thanhtuan2503/digitalSystemBoard/digitalSystemBoard/3dSymbol/Fuse.step

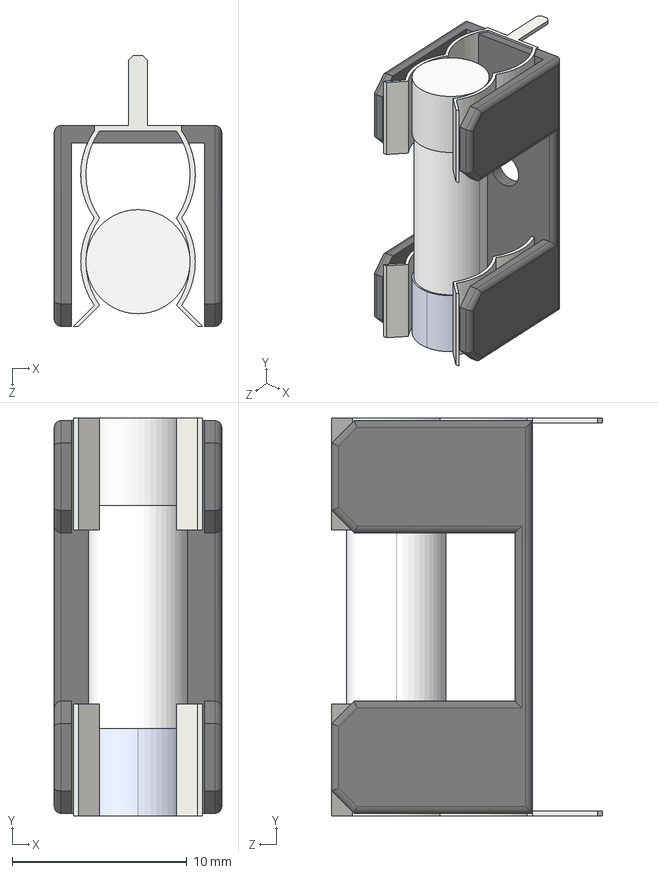
[picture p18: CAD file, 2022-01-30]
digitalSystemBoard/3dSymbol/Fuse.step
9.60 x 22.8 x 15.5 mm
Fuseholder_Cylinder-5x20mm_Schurter_0031_8201_Horizontal_Open
FuseTube^Fuse
