thanhtuan2503/digitalSystemBoard/digitalSystemBoard/3dSymbol/DS1013 (IDC CONNFLY)/DS1013-50S (IDC-50MS CONNFLY).step

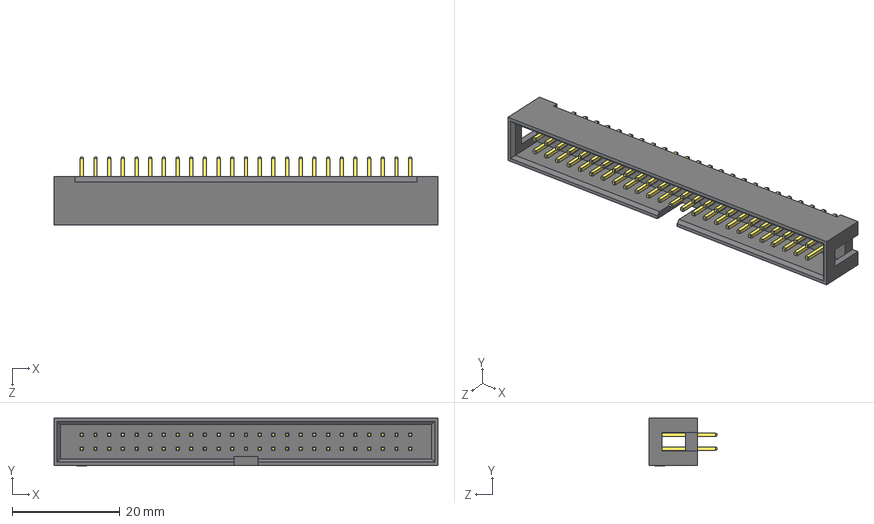
[picture p19: CAD file, 2022-01-30]
digitalSystemBoard/3dSymbol/DS1013 (IDC CONNFLY)/DS1013-50S (IDC-50MS CONNFLY).step
71.3 x 8.90 x 12.6 mm
