thanhtuan2503/digitalSystemBoard/digitalSystemBoard/3dSymbol/DS1013 (IDC CONNFLY)/DS1013-20S (IDC-20MS CONNFLY).stp

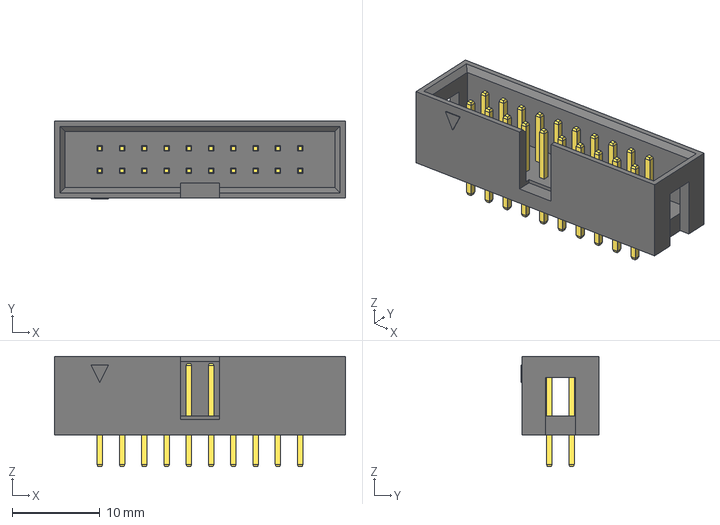
[picture p20: CAD file, 2022-01-30]
digitalSystemBoard/3dSymbol/DS1013 (IDC CONNFLY)/DS1013-20S (IDC-20MS CONNFLY).stp
33.2 x 8.90 x 12.6 mm
