thanhtuan2503/digitalSystemBoard/digitalSystemBoard/3dSymbol/Modul3d_V3.step

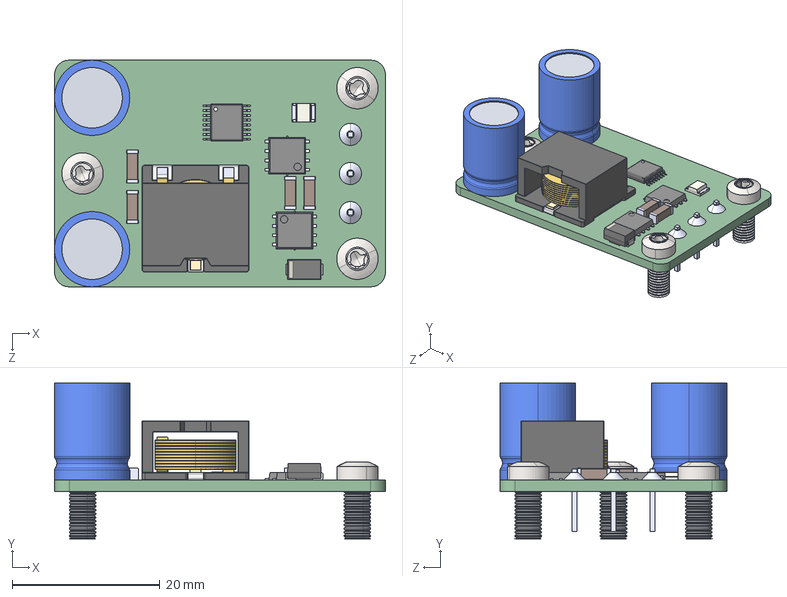
[picture p21: CAD file, 2022-01-30]
digitalSystemBoard/3dSymbol/Modul3d_V3.step
44.9 x 21.1 x 30.7 mm
Part1.step
Inductor.step
TPCA8053-H.step x 2
tu.step x 2
TPS40057PWPRG4.step
D_SMA.step
LED_1210_3225Metric.step
tu_Lon.step x 4
hexalobular socket pan head_iso_ISO 14583 - M3 x 8 x 7 - 4.8-S x 3
Solder^Modul3d
