thanhtuan2503/digitalSystemBoard/digitalSystemBoard/3dSymbol/DS1013 (IDC CONNFLY)/DS1013-26S (IDC-26MS CONNFLY).stp

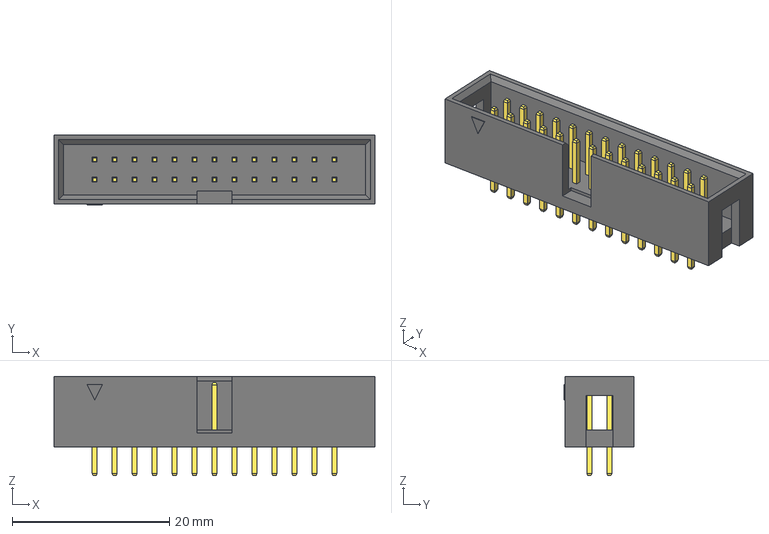
[picture p22: CAD file, 2022-01-30]
digitalSystemBoard/3dSymbol/DS1013 (IDC CONNFLY)/DS1013-26S (IDC-26MS CONNFLY).stp
40.8 x 8.90 x 12.6 mm
