thanhtuan2503/digitalSystemBoard/digitalSystemBoard/3dSymbol/Tactal-Switch-SMD-12mmx12mmx4.3mm_V2.step

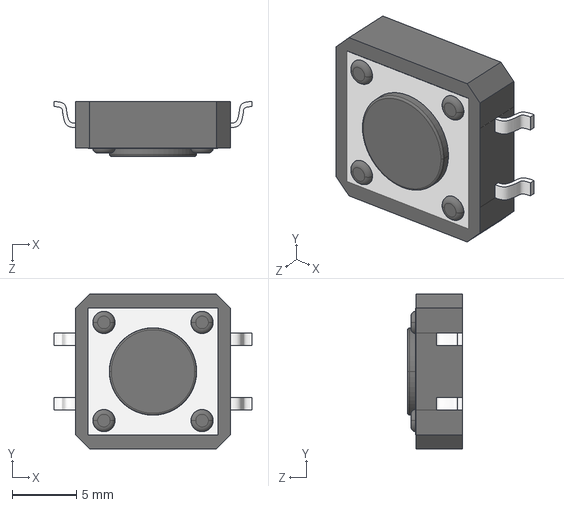
[picture p23: CAD file, 2022-01-30]
digitalSystemBoard/3dSymbol/Tactal-Switch-SMD-12mmx12mmx4.3mm_V2.step
15.4 x 12.0 x 4.25 mm
