thanhtuan2503/digitalSystemBoard/digitalSystemBoard/3dSymbol/DS1013 (IDC CONNFLY)/DS1013-6S (IDC-6MS CONNFLY).stp

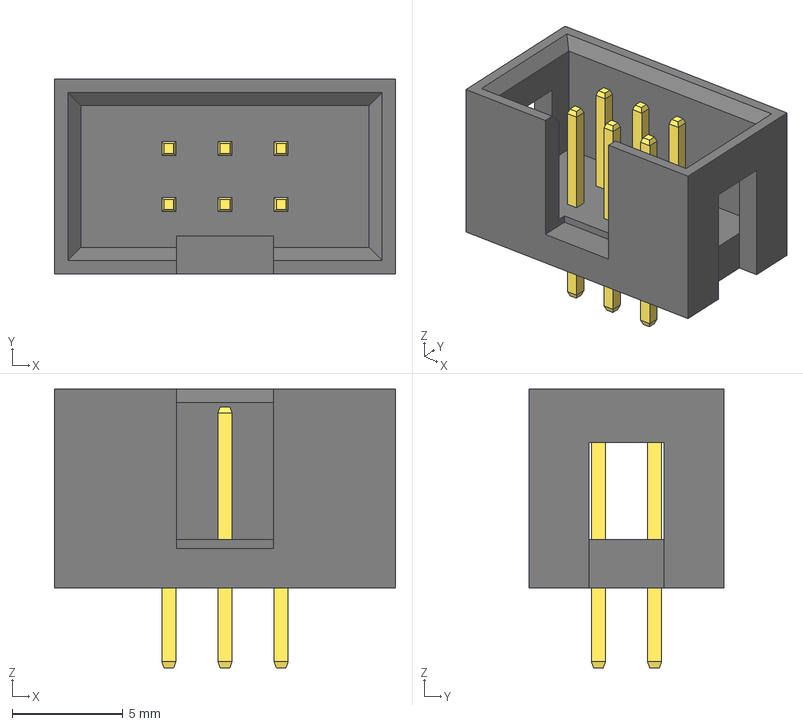
[picture p24: CAD file, 2022-01-30]
digitalSystemBoard/3dSymbol/DS1013 (IDC CONNFLY)/DS1013-6S (IDC-6MS CONNFLY).stp
15.4 x 8.80 x 12.6 mm
