thanhtuan2503/digitalSystemBoard/digitalSystemBoard/3dSymbol/DS1013 (IDC CONNFLY)/DS1013-64S (IDC-64MS CONNFLY).step

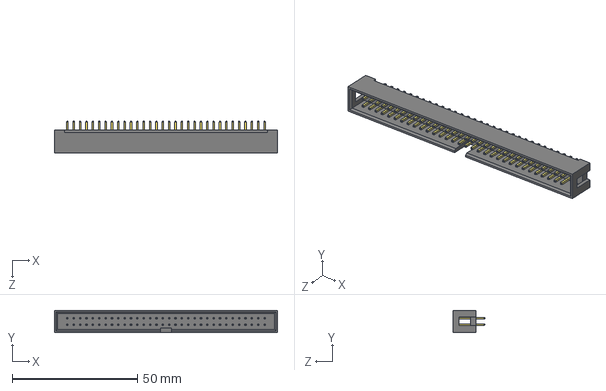
[picture p25: CAD file, 2022-01-30]
digitalSystemBoard/3dSymbol/DS1013 (IDC CONNFLY)/DS1013-64S (IDC-64MS CONNFLY).step
89.1 x 8.90 x 12.6 mm
