thanhtuan2503/digitalSystemBoard/digitalSystemBoard/3dSymbol/DS1013 (IDC CONNFLY)/DS1013-34S (IDC-34MS CONNFLY).step

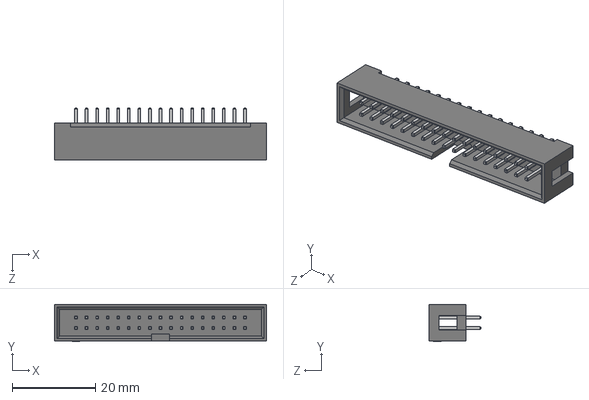
[picture p26: CAD file, 2022-01-30]
digitalSystemBoard/3dSymbol/DS1013 (IDC CONNFLY)/DS1013-34S (IDC-34MS CONNFLY).step
51.0 x 8.90 x 12.6 mm
