thanhtuan2503/digitalSystemBoard/digitalSystemBoard/3dSymbol/DS1013 (IDC CONNFLY)/DS1013-60S (IDC-60MS CONNFLY).step

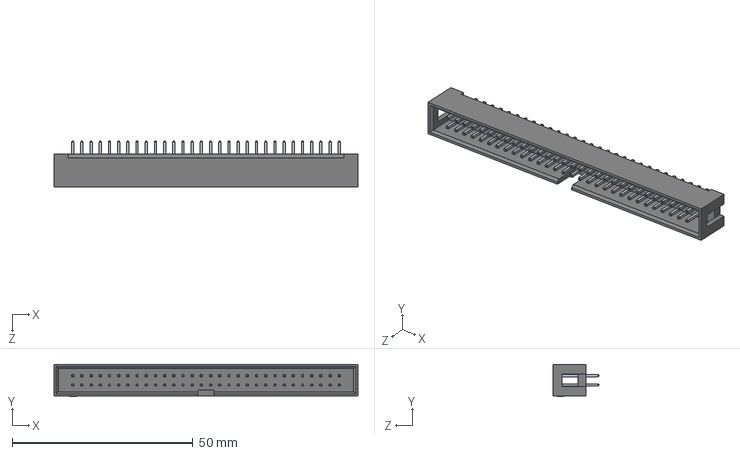
[picture p27: CAD file, 2022-01-30]
digitalSystemBoard/3dSymbol/DS1013 (IDC CONNFLY)/DS1013-60S (IDC-60MS CONNFLY).step
84.0 x 8.90 x 12.6 mm
