thanhtuan2503/digitalSystemBoard/digitalSystemBoard/3dSymbol/PowerSwitch_V2.step

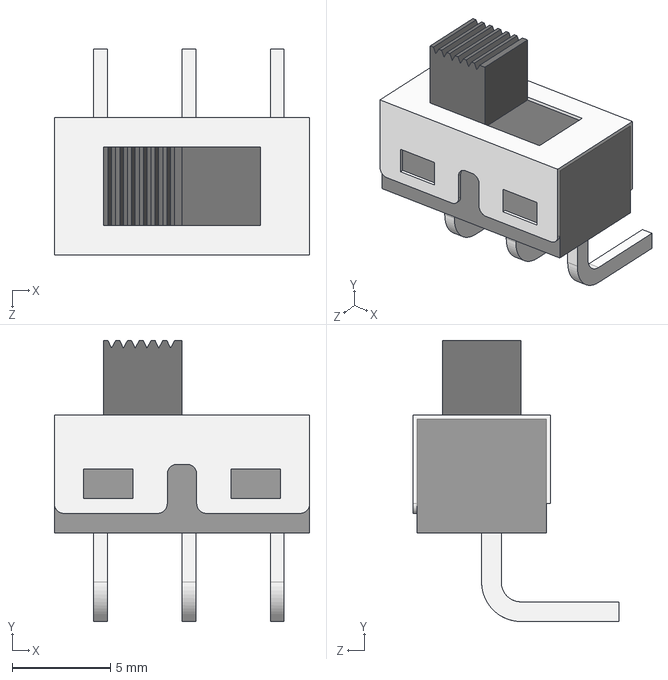
[picture p28: CAD file, 2022-01-30]
digitalSystemBoard/3dSymbol/PowerSwitch_V2.step
13.0 x 14.3 x 10.5 mm
