thanhtuan2503/digitalSystemBoard/digitalSystemBoard/3dSymbol/BC847BW,115.STEP

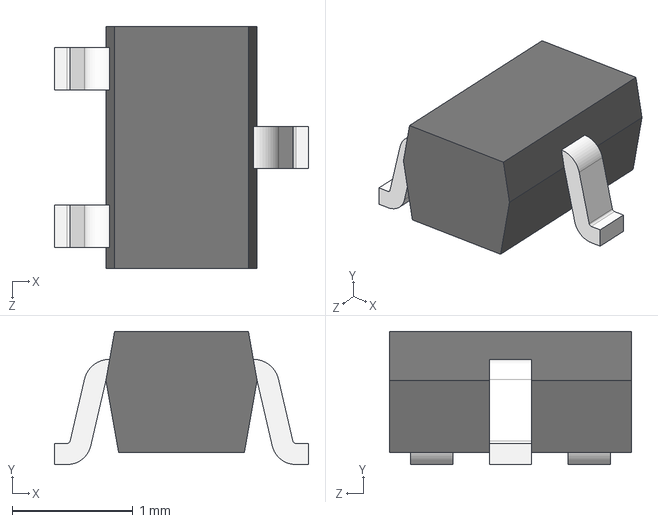
[picture p29: CAD file, 2022-01-30]
digitalSystemBoard/3dSymbol/BC847BW,115.STEP
2.10 x 1.10 x 2.00 mm
