thanhtuan2503/digitalSystemBoard/digitalSystemBoard/3dSymbol/Modul3d.step

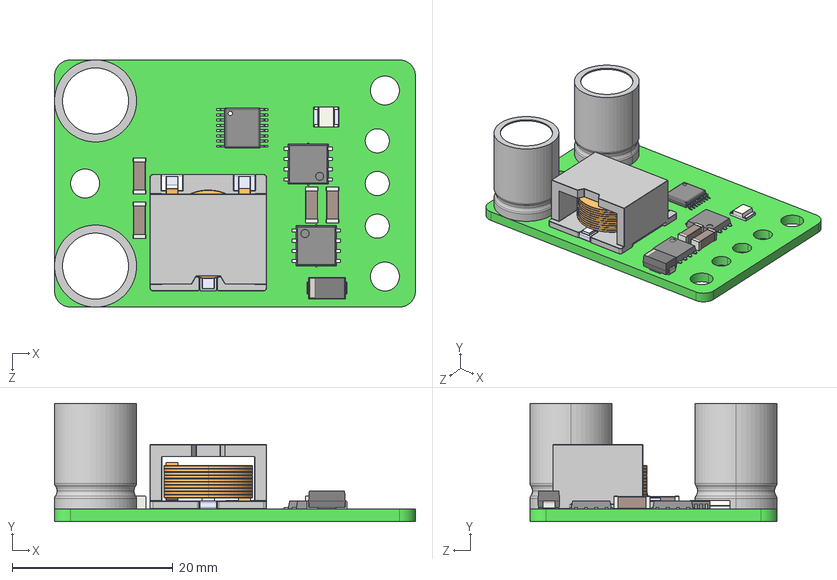
[picture p30: CAD file, 2022-01-30]
digitalSystemBoard/3dSymbol/Modul3d.step
44.9 x 14.7 x 30.7 mm
Inductor
TPCA8053-H x 2
tu x 2
TPS40057PWPRG4
D_SMA
LED_1210_3225Metric
tu_Lon x 4
