thanhtuan2503/digitalSystemBoard/digitalSystemBoard/3dSymbol/DIP_16_PIN_SOCKET.stp

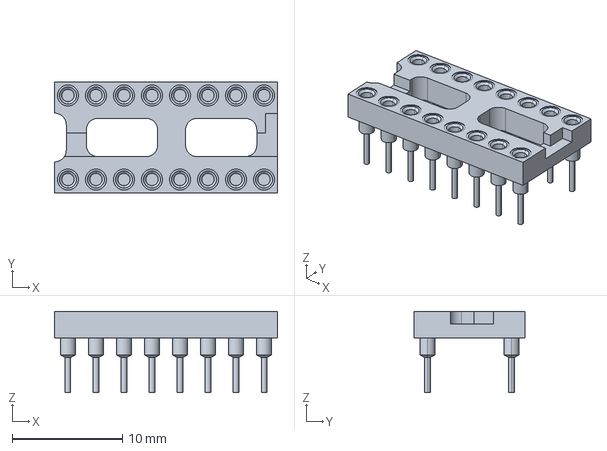
[picture p31: CAD file, 2022-01-30]
digitalSystemBoard/3dSymbol/DIP_16_PIN_SOCKET.stp
20.2 x 10.1 x 7.37 mm
