thanhtuan2503/digitalSystemBoard/digitalSystemBoard/3dSymbol/SC70-6.step

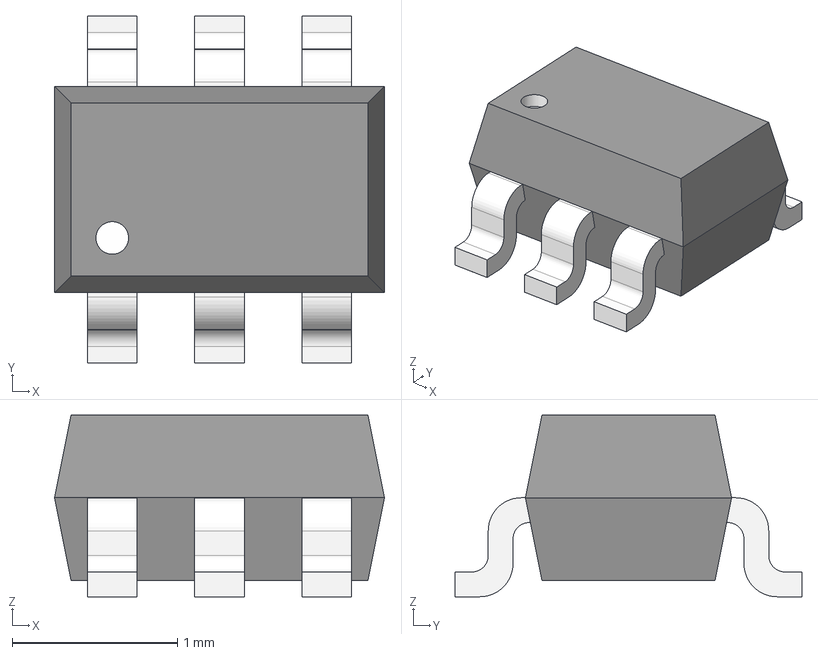
[picture p32: CAD file, 2022-01-30]
digitalSystemBoard/3dSymbol/SC70-6.step
2.00 x 2.10 x 1.10 mm
