thanhtuan2503/digitalSystemBoard/digitalSystemBoard/3dSymbol/FBMH2012HM800-T.STEP

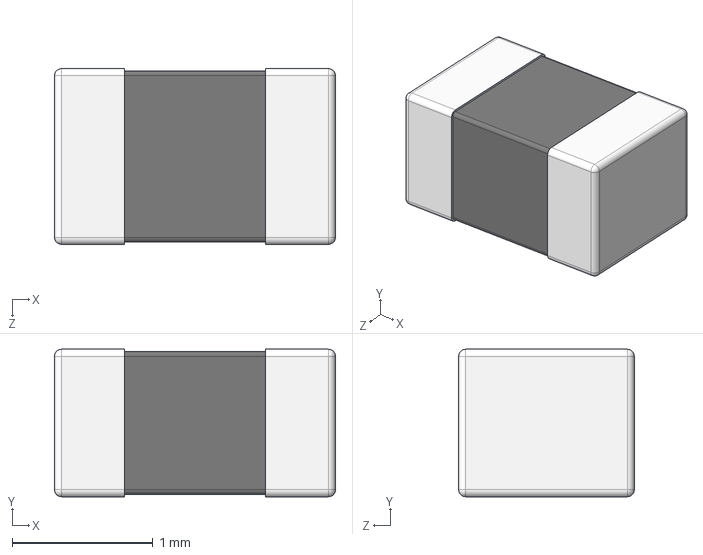
[picture p33: CAD file, 2022-01-30]
digitalSystemBoard/3dSymbol/FBMH2012HM800-T.STEP
2.00 x 1.05 x 1.25 mm
