thanhtuan2503/digitalSystemBoard/digitalSystemBoard/3dSymbol/LM358M.STEP

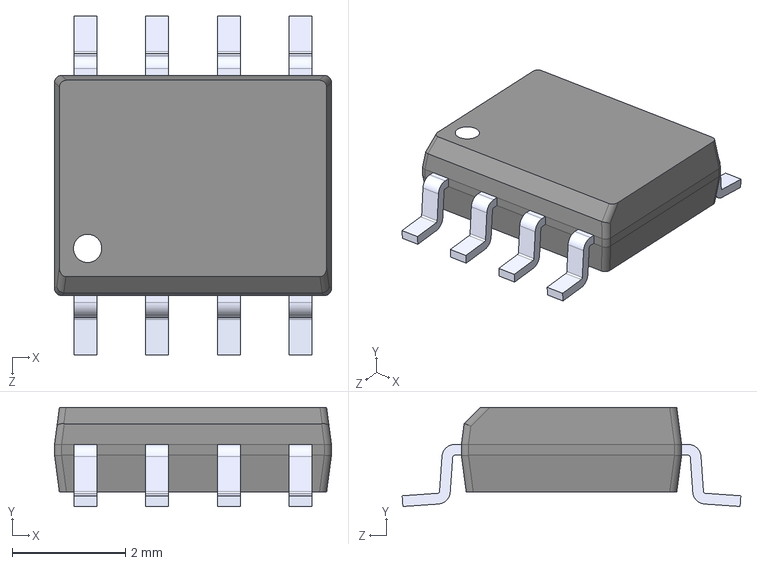
[picture p34: CAD file, 2020-10-29]
digitalSystemBoard/3dSymbol/LM358M.STEP
4.90 x 1.75 x 5.99 mm
