thanhtuan2503/digitalSystemBoard/digitalSystemBoard/3dSymbol/R-PDSO-G4.STEP

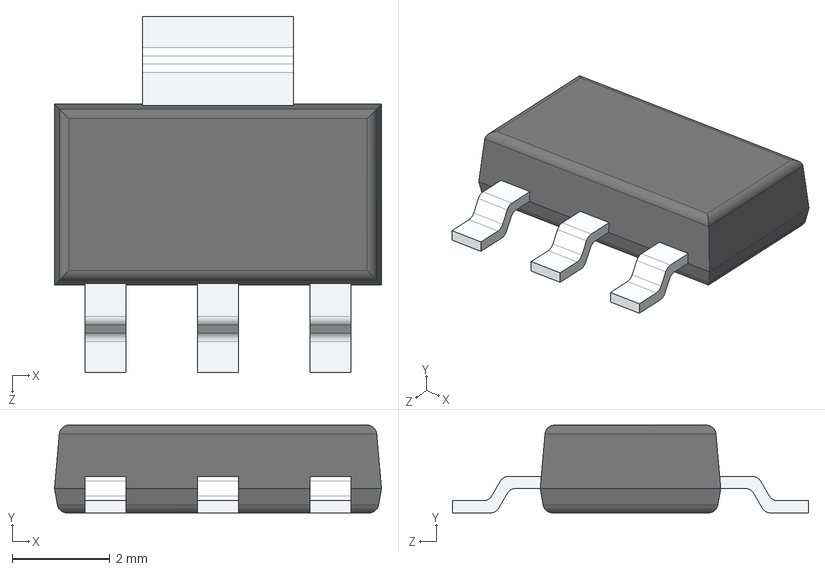
[picture p35: CAD file, 2020-10-24]
digitalSystemBoard/3dSymbol/R-PDSO-G4.STEP
6.70 x 1.80 x 7.30 mm
