thanhtuan2503/digitalSystemBoard/digitalSystemBoard/3dSymbol/to252-3_p4-56_l6-54_w6-04.stp

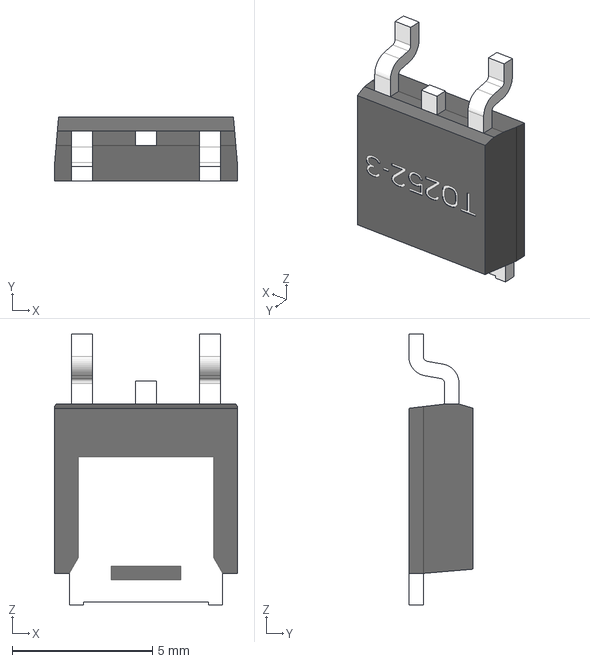
[picture p36: CAD file, 2020-10-24]
digitalSystemBoard/3dSymbol/to252-3_p4-56_l6-54_w6-04.stp
6.54 x 2.30 x 9.67 mm
