thanhtuan2503/digitalSystemBoard/digitalSystemBoard/3dSymbol/SMF05C.STEP

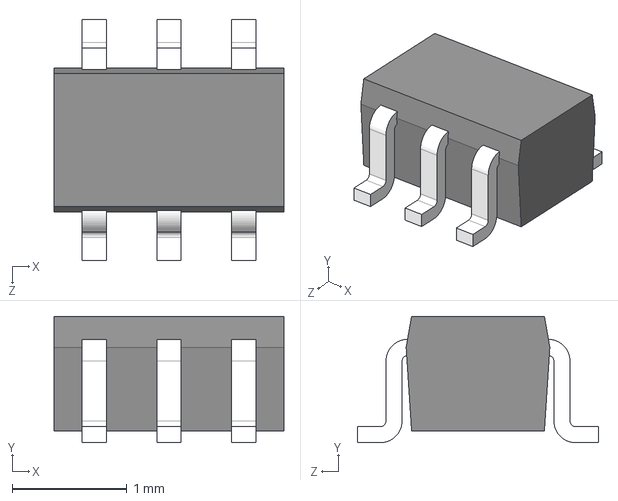
[picture p37: CAD file, 2020-10-22]
digitalSystemBoard/3dSymbol/SMF05C.STEP
2.00 x 1.10 x 2.10 mm
