thanhtuan2503/digitalSystemBoard/digitalSystemBoard/3dSymbol/fdn340p.stp

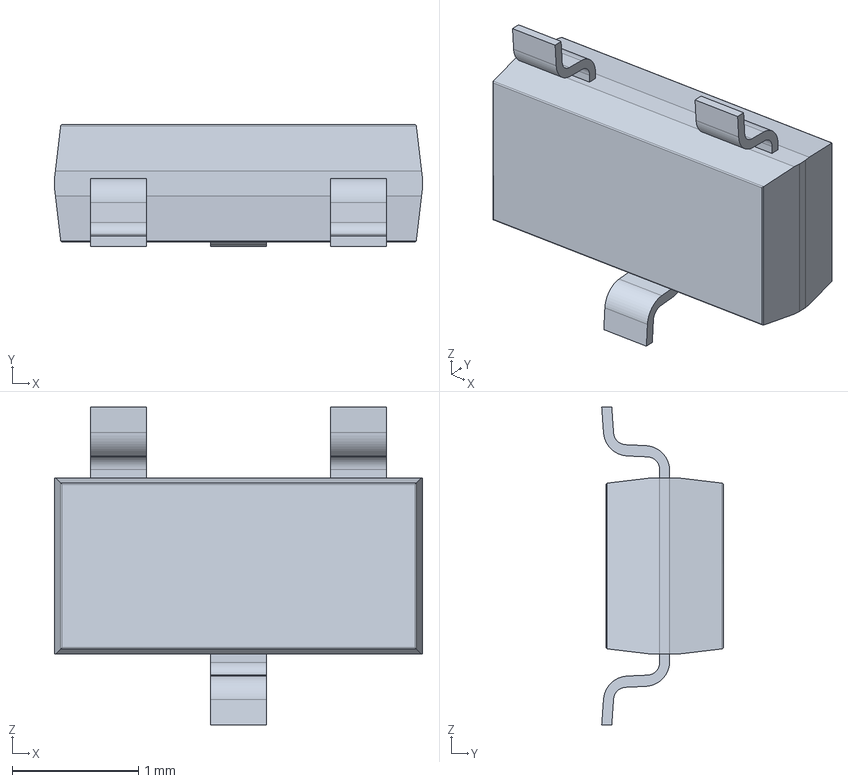
[picture p38: CAD file, 2020-10-21]
digitalSystemBoard/3dSymbol/fdn340p.stp
2.92 x 0.965 x 2.52 mm
