thanhtuan2503/digitalSystemBoard/digitalSystemBoard/3dSymbol/LP2985-33DBVRG4.STEP

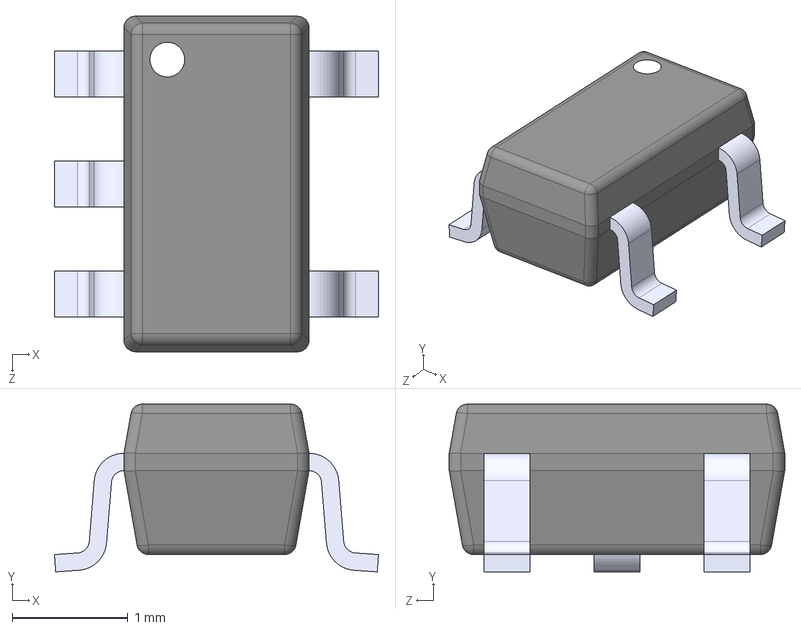
[picture p39: CAD file, 2020-10-21]
digitalSystemBoard/3dSymbol/LP2985-33DBVRG4.STEP
2.80 x 1.45 x 2.90 mm
