thanhtuan2503/digitalSystemBoard/digitalSystemBoard/3dSymbol/OSC5032.STEP

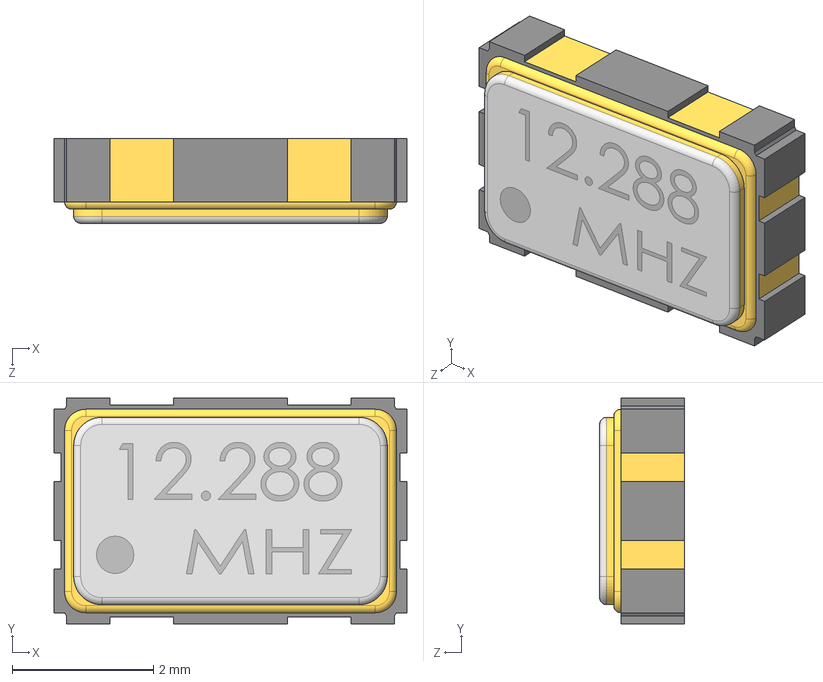
[picture p40: CAD file, 2020-10-21]
digitalSystemBoard/3dSymbol/OSC5032.STEP
5.00 x 3.20 x 1.20 mm
