thanhtuan2503/digitalSystemBoard/digitalSystemBoard/3dSymbol/LMV358AIDGKR.STEP

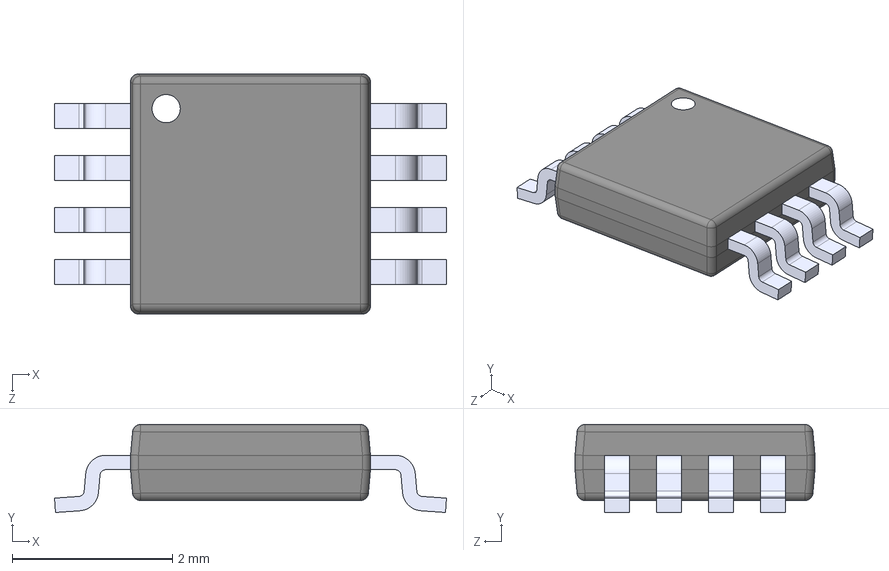
[picture p41: CAD file, 2020-10-21]
digitalSystemBoard/3dSymbol/LMV358AIDGKR.STEP
4.90 x 1.10 x 3.00 mm
