thanhtuan2503/digitalSystemBoard/digitalSystemBoard/3dSymbol/Fuseholder_Cylinder-5x20mm_Schurter_0031_8201_Horizontal_Open.step

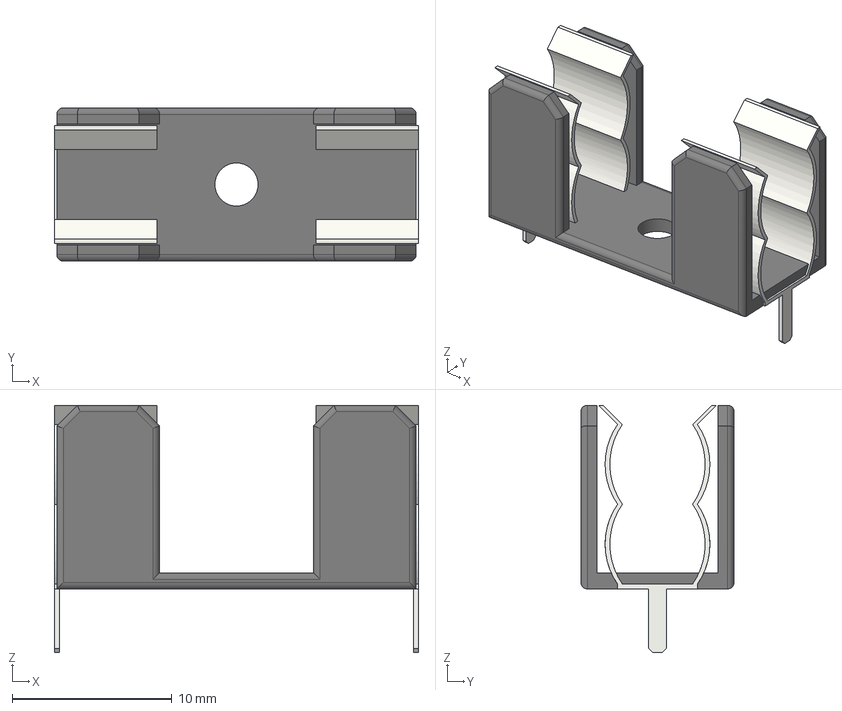
[picture p42: CAD file, 2020-10-21]
digitalSystemBoard/3dSymbol/Fuseholder_Cylinder-5x20mm_Schurter_0031_8201_Horizontal_Open.step
22.8 x 9.60 x 15.5 mm
