thanhtuan2503/digitalSystemBoard/digitalSystemBoard/3dSymbol/LM317T.STEP

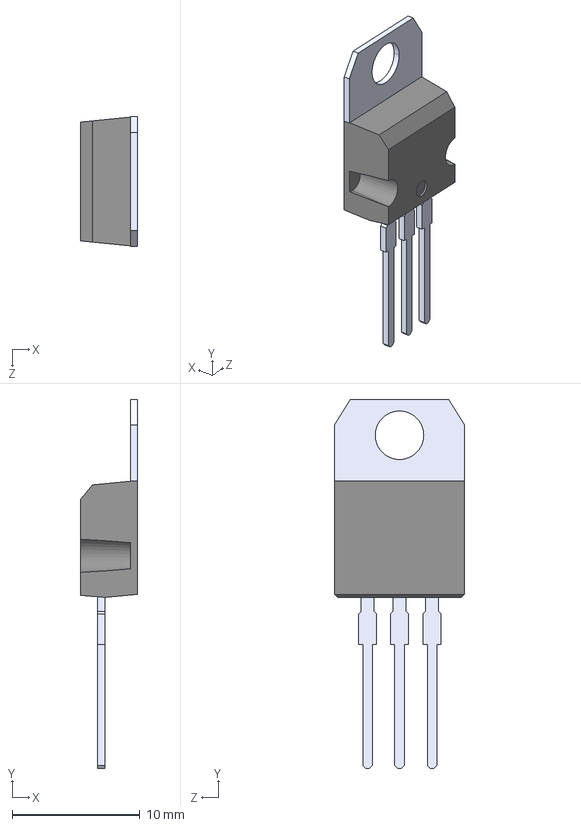
[picture p43: CAD file, 2020-10-21]
digitalSystemBoard/3dSymbol/LM317T.STEP
4.50 x 28.9 x 10.2 mm
