thanhtuan2503/digitalSystemBoard/digitalSystemBoard/3dSymbol/R_Axial_Power_L20.0mm_W6.4mm_P22.40mm.step

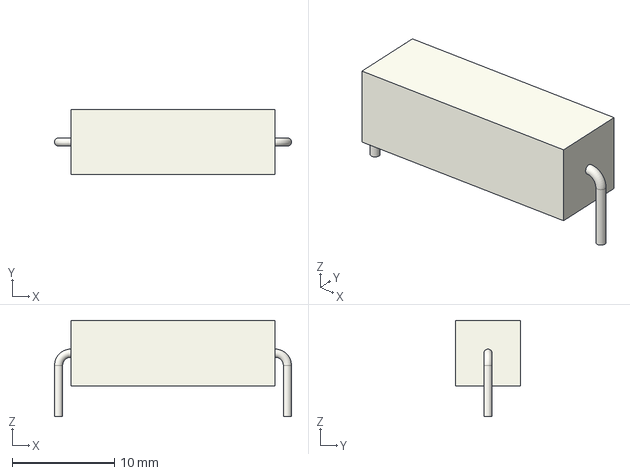
[picture p44: CAD file, 2020-10-21]
digitalSystemBoard/3dSymbol/R_Axial_Power_L20.0mm_W6.4mm_P22.40mm.step
23.2 x 6.40 x 9.40 mm
