thanhtuan2503/digitalSystemBoard/digitalSystemBoard/3dSymbol/heatsink_to220_aluminum.STEP

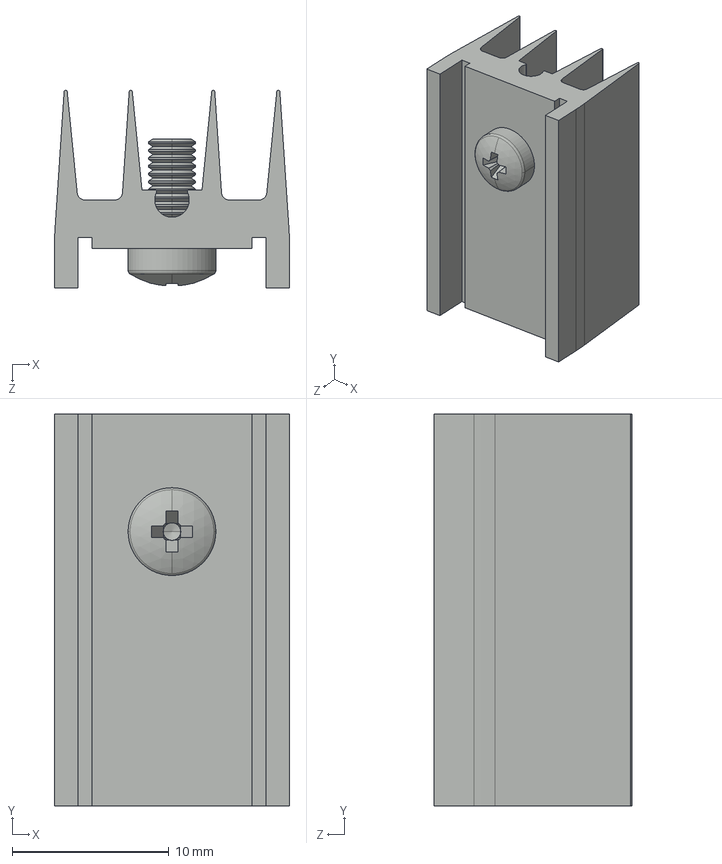
[picture p45: CAD file, 2020-10-20]
digitalSystemBoard/3dSymbol/heatsink_to220_aluminum.STEP
15.0 x 25.0 x 12.6 mm
heatsink
pan head cross recess screw_iso_ISO 7045 - M3 x 6 - Z - 6S
