thanhtuan2503/digitalSystemBoard/digitalSystemBoard/3dSymbol/EG1249.step

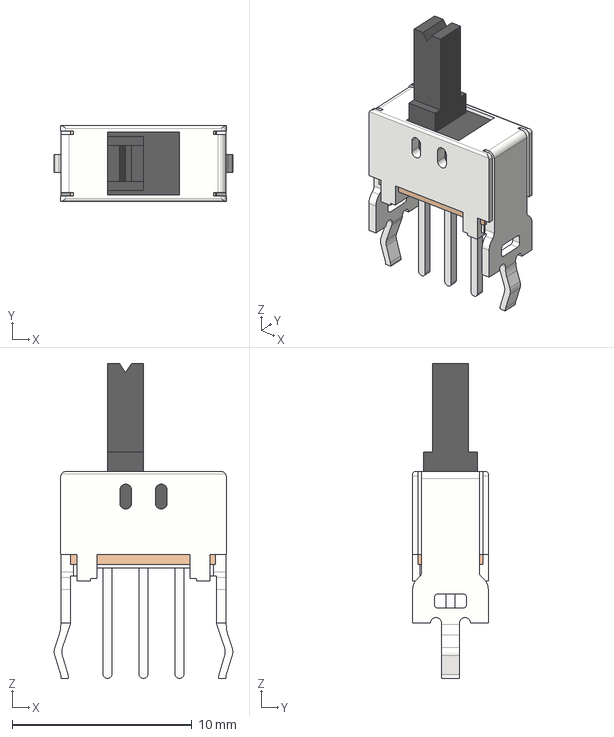
[picture p46: CAD file, 2020-10-20]
digitalSystemBoard/3dSymbol/EG1249.step
9.93 x 4.20 x 17.5 mm
