thanhtuan2503/digitalSystemBoard/digitalSystemBoard/3dSymbol/ST-LM317T.stp

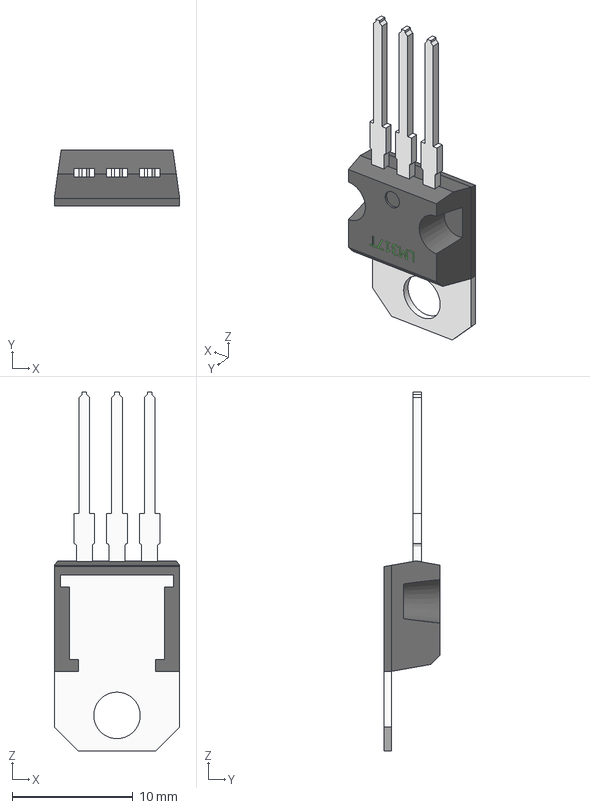
[picture p47: CAD file, 2020-10-20]
digitalSystemBoard/3dSymbol/ST-LM317T.stp
10.4 x 4.60 x 29.8 mm
