thanhtuan2503/digitalSystemBoard/digitalSystemBoard/3dSymbol/RK09K1130AH1.STEP

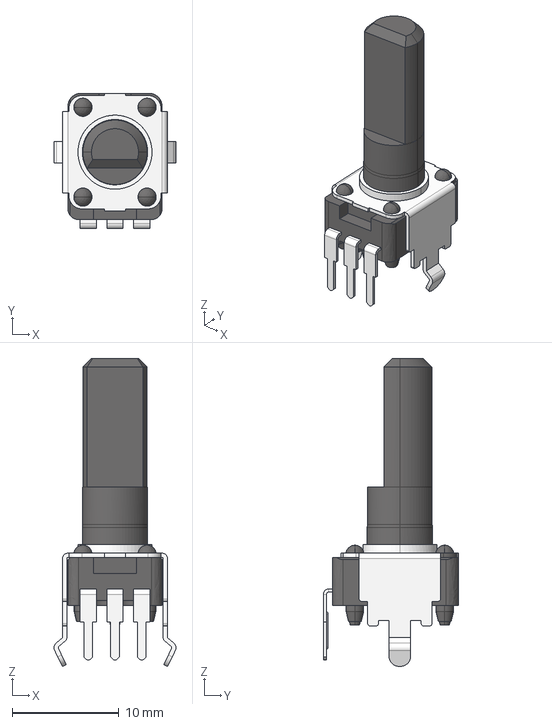
[picture p48: CAD file, 2020-10-19]
digitalSystemBoard/3dSymbol/RK09K1130AH1.STEP
11.4 x 12.7 x 28.8 mm
