thanhtuan2503/digitalSystemBoard/digitalSystemBoard/3dSymbol/Power Barrel Connector Jack 694106301002.stp

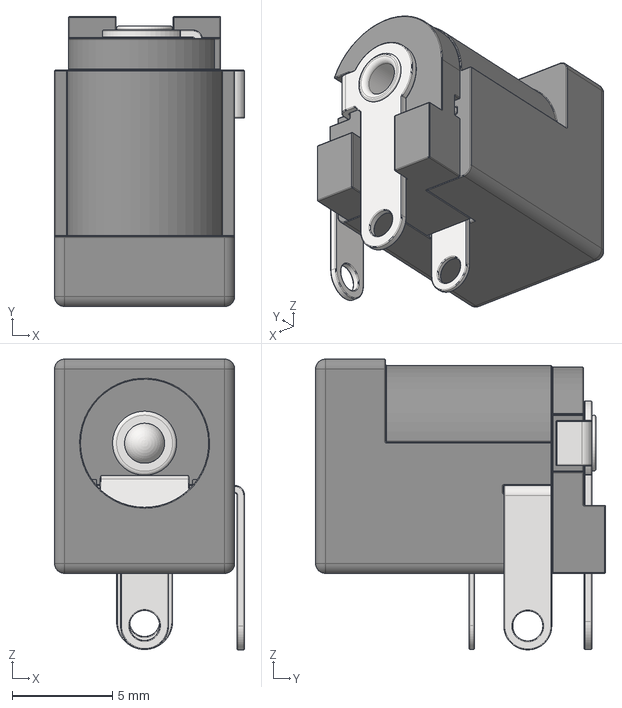
[picture p49: CAD file, 2020-10-19]
digitalSystemBoard/3dSymbol/Power Barrel Connector Jack 694106301002.stp
9.49 x 14.5 x 14.5 mm
