thanhtuan2503/digitalSystemBoard/digitalSystemBoard/3dSymbol/Tactal Switch - SMD (12mmx12mmx9.5mm).stp

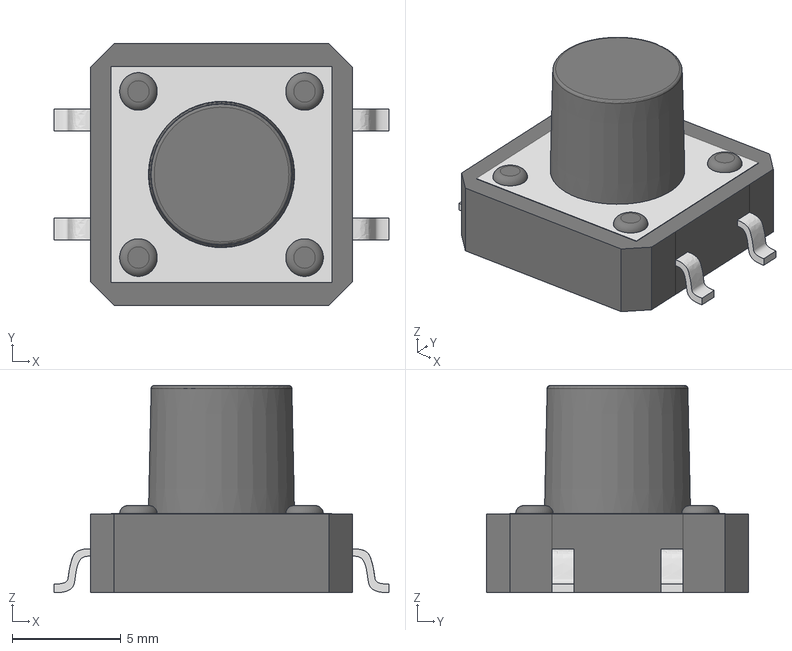
[picture p50: CAD file, 2020-10-19]
digitalSystemBoard/3dSymbol/Tactal Switch - SMD (12mmx12mmx9.5mm).stp
15.4 x 12.0 x 9.50 mm
