thanhtuan2503/digitalSystemBoard/digitalSystemBoard/3dSymbol/SN74LS47N.STEP

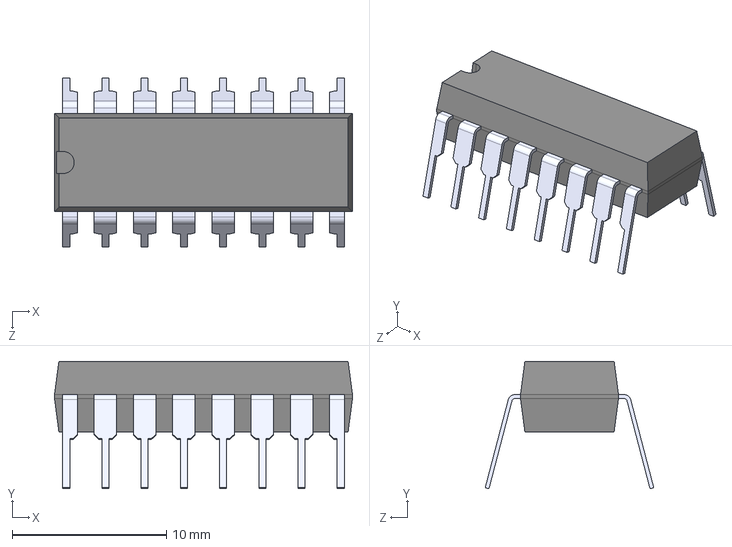
[picture p51: CAD file, 2020-10-19]
digitalSystemBoard/3dSymbol/SN74LS47N.STEP
19.3 x 8.25 x 10.9 mm
