thanhtuan2503/digitalSystemBoard/digitalSystemBoard/3dSymbol/Tactal Switch - SMD (12mmx12mmx10.0mm).stp

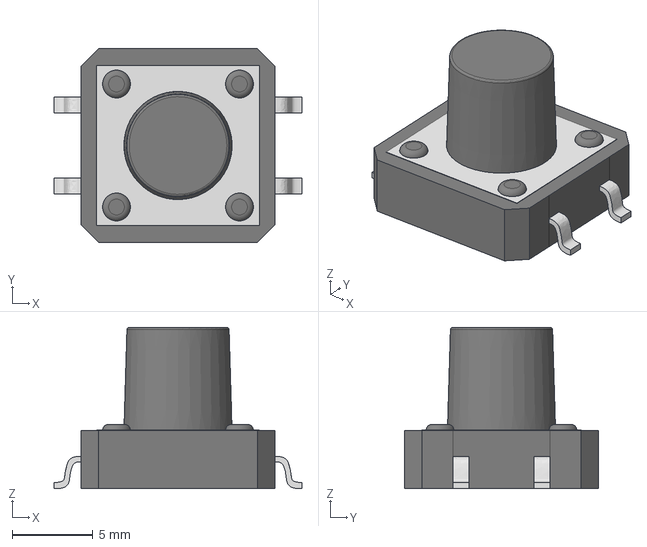
[picture p55: CAD file, 2020-10-19]
digitalSystemBoard/3dSymbol/Tactal Switch - SMD (12mmx12mmx10.0mm).stp
15.4 x 12.0 x 10.0 mm
