thanhtuan2503/digitalSystemBoard/digitalSystemBoard/3dSymbol/3296W-1-501.STEP

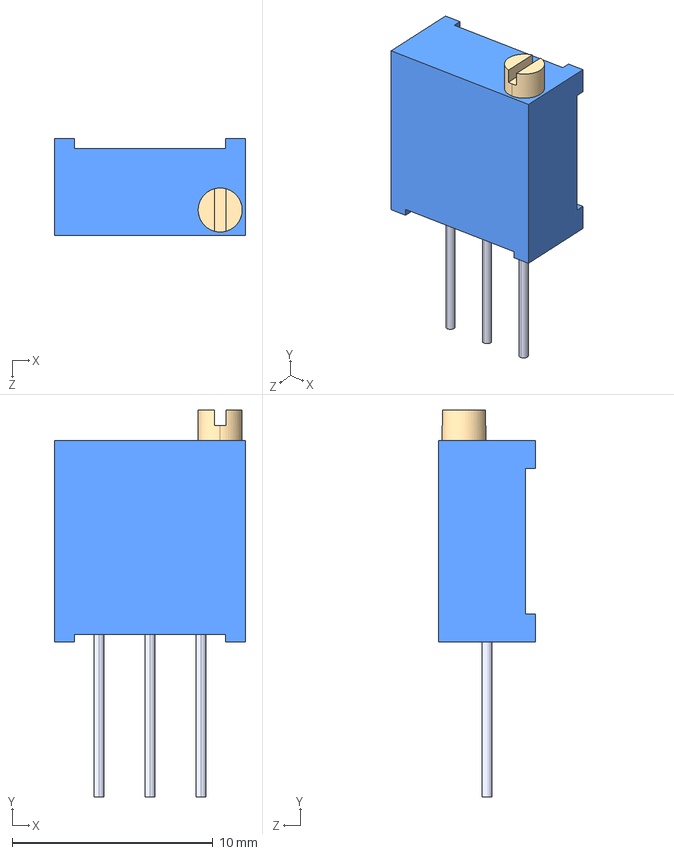
[picture p63: CAD file, 2020-10-14]
digitalSystemBoard/3dSymbol/3296W-1-501.STEP
9.53 x 19.3 x 4.83 mm
