thanhtuan2503/digitalSystemBoard/digitalSystemBoard/3dSymbol/3528 SMD LED.stp

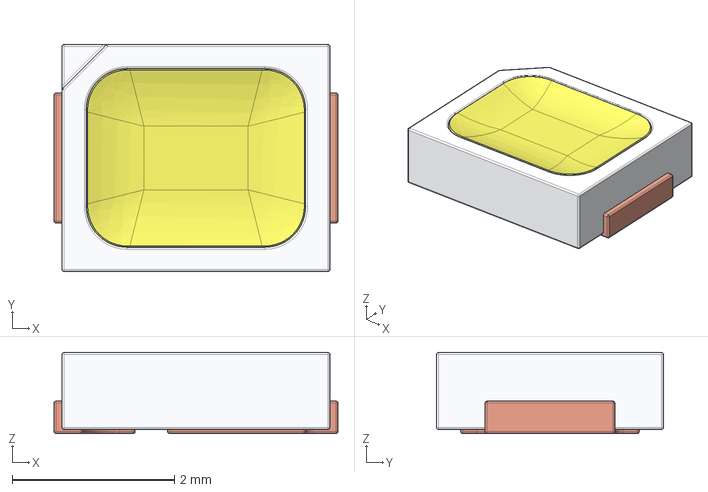
[picture p64: CAD file, 2020-10-14]
digitalSystemBoard/3dSymbol/3528 SMD LED.stp
3.50 x 2.80 x 1.00 mm
