thanhtuan2503/digitalSystemBoard/digitalSystemBoard/3dSymbol/2N7002--3DModel-STEP-56544.STEP

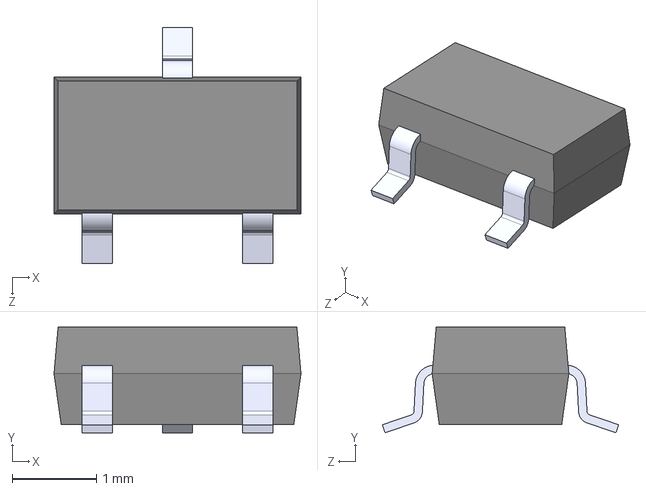
[picture p65: CAD file, 2020-10-14]
digitalSystemBoard/3dSymbol/2N7002--3DModel-STEP-56544.STEP
2.93 x 1.25 x 2.80 mm
