thanhtuan2503/digitalSystemBoard/digitalSystemBoard/3dSymbol/MJD122T4G.STEP

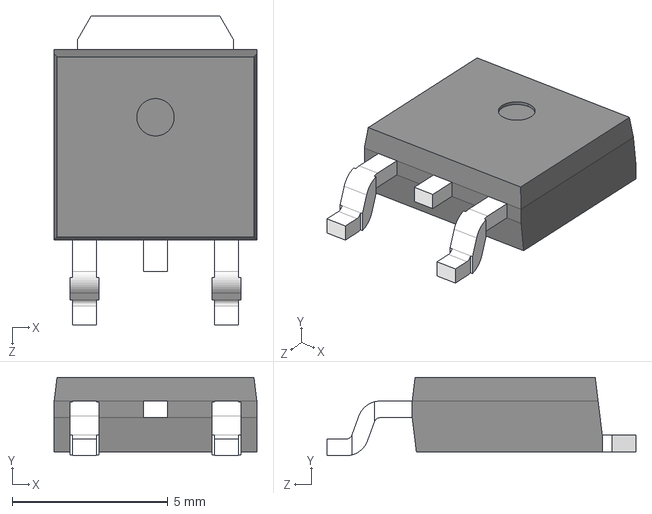
[picture p66: CAD file, 2020-10-14]
digitalSystemBoard/3dSymbol/MJD122T4G.STEP
6.50 x 2.51 x 9.91 mm
